DragosFromea/eBook-Reader-TSC/Images/Screenshot 2025-04-06 184918.png

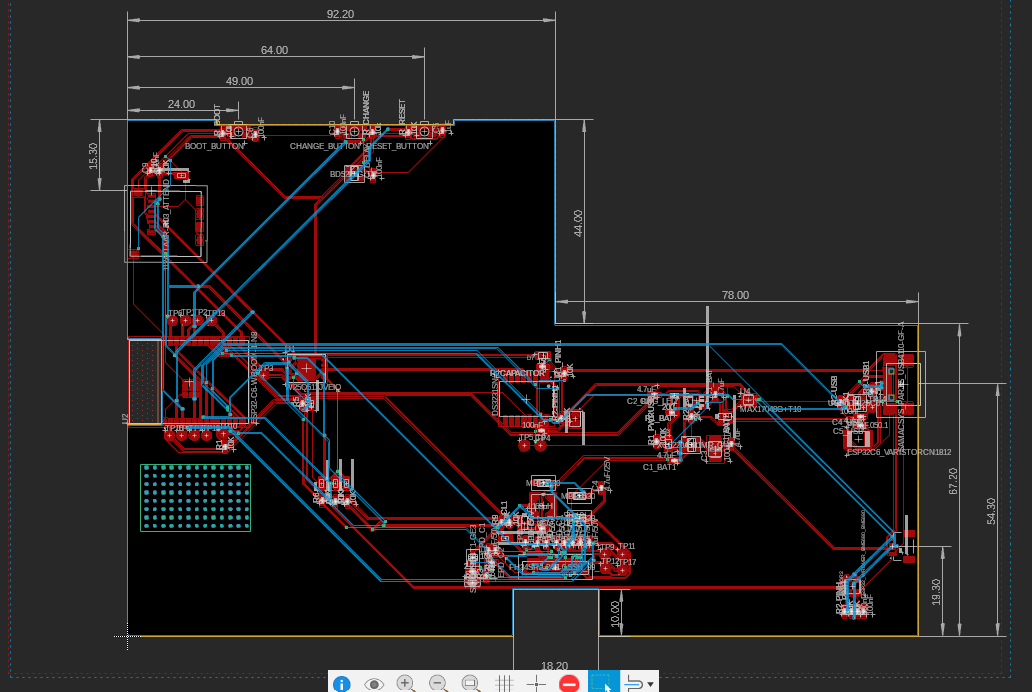
Images/Screenshot 2025-04-06 184918.png
