DragosFromea/eBook-Reader-TSC/Images/Screenshot 2025-04-06 185648.png

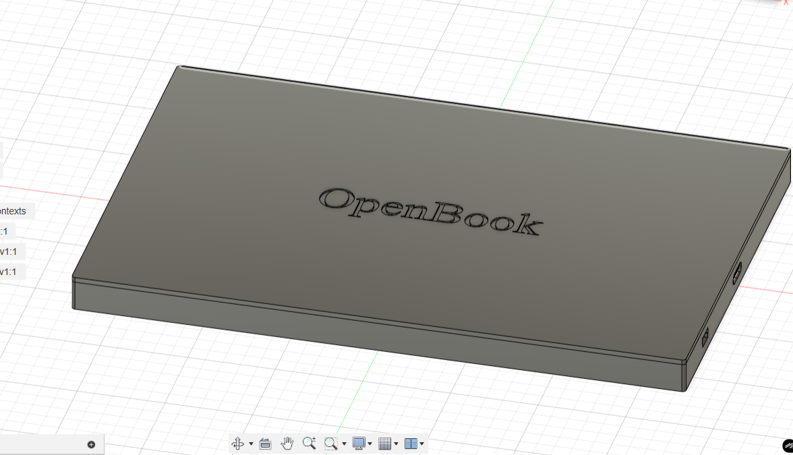
Images/Screenshot 2025-04-06 185648.png
