DragosFromea/eBook-Reader-TSC/Images/Screenshot 2025-04-06 185721.png

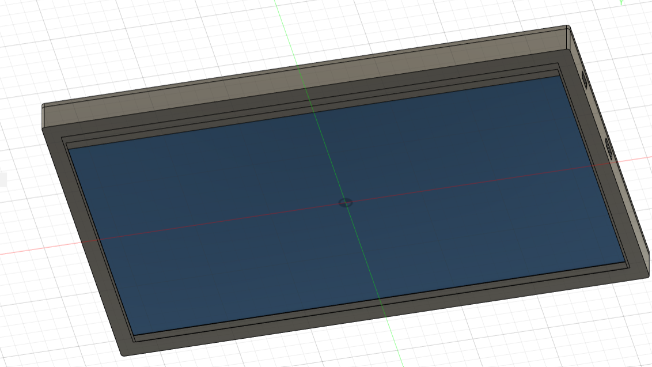
Images/Screenshot 2025-04-06 185721.png
